LukasKropf/IO-Link-Shield/KiCad/ExportBilder/20171119_PCB_Vorschau_Unten.png

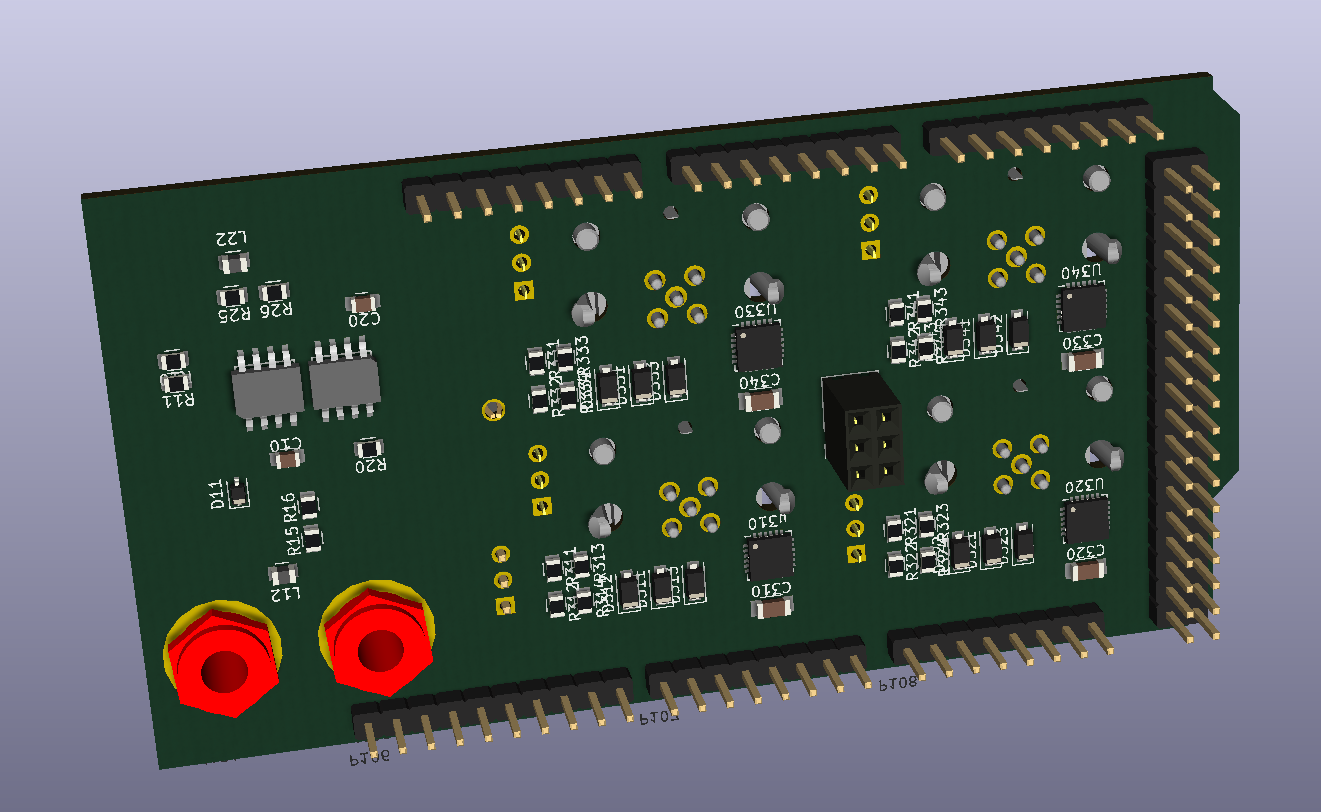
KiCad/ExportBilder/20171119_PCB_Vorschau_Unten.png
