LukasKropf/IO-Link-Shield/KiCad/ExportBilder/20171201_PCB_Vorschau_oben.png

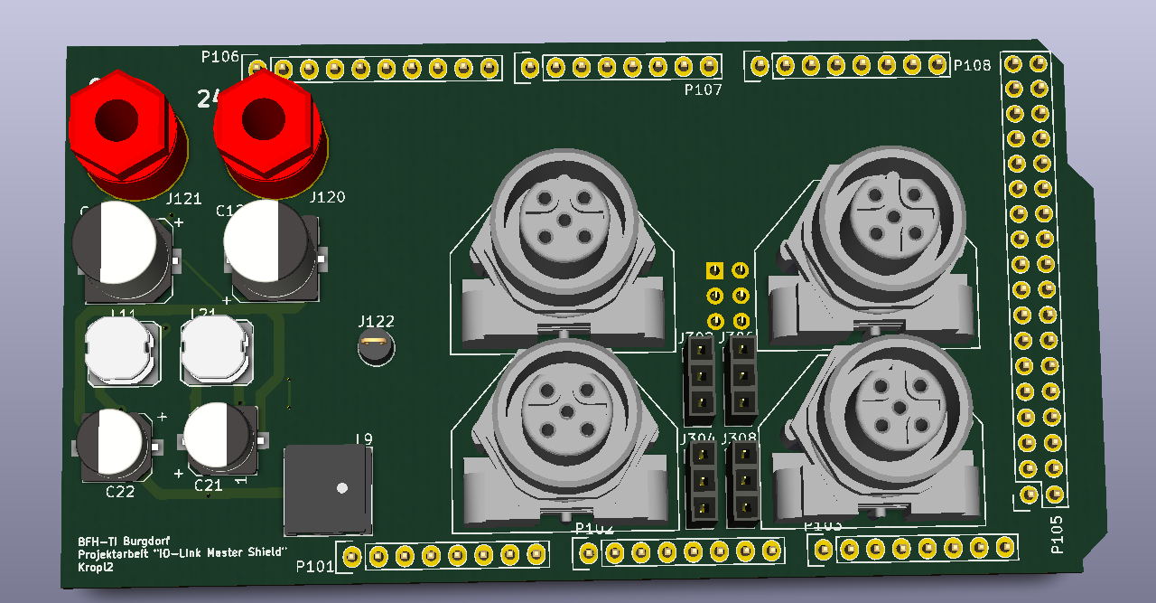
KiCad/ExportBilder/20171201_PCB_Vorschau_oben.png
