LukasKropf/IO-Link-Shield/KiCad/ExportBilder/20171201_PCB_Vorschau_Unten.png

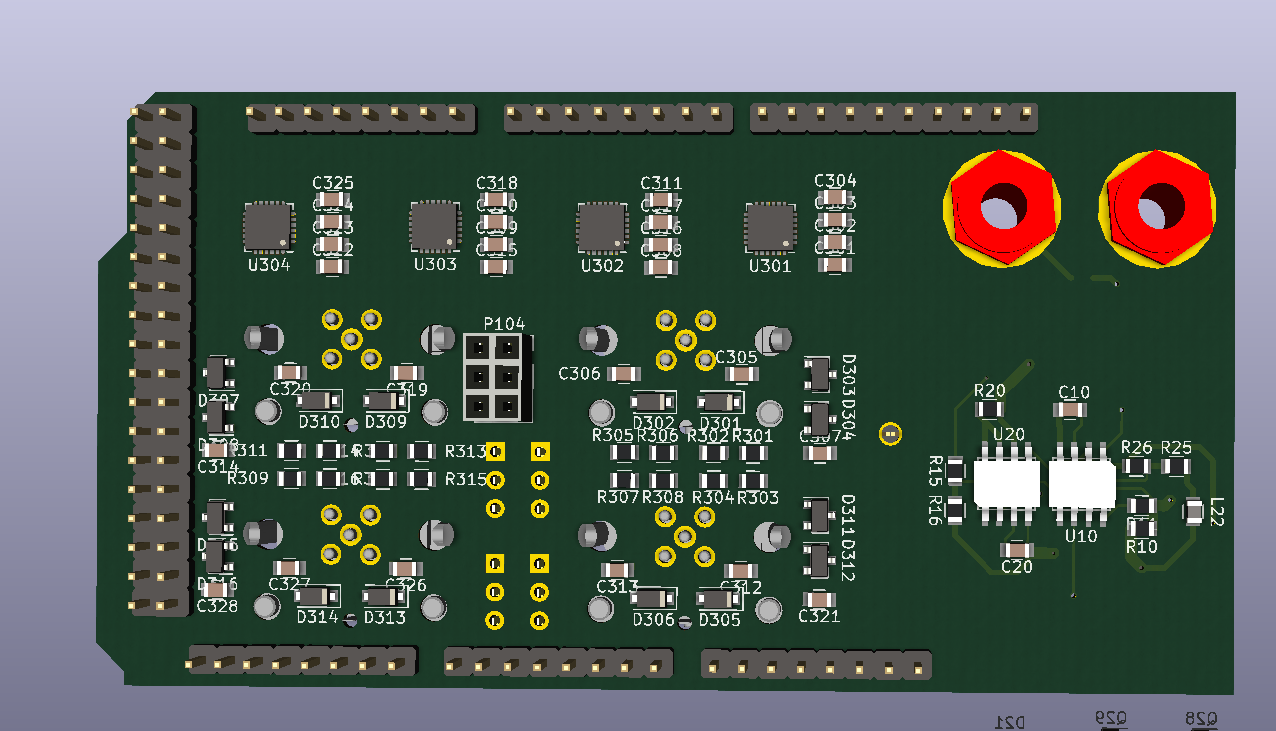
KiCad/ExportBilder/20171201_PCB_Vorschau_Unten.png
