LukasKropf/IO-Link-Shield/KiCad/ExportBilder/TestPoint.png

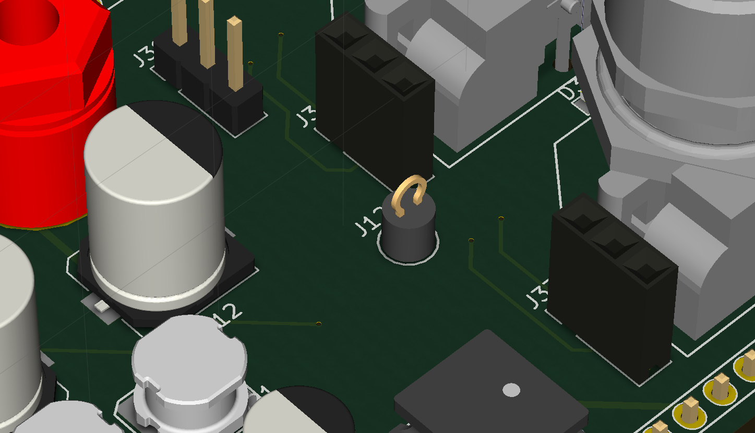
KiCad/ExportBilder/TestPoint.png
