LukasKropf/IO-Link-Shield/Simulationen/BuckBoostConverter/BoostConverter.asc

Arduino: res; 50
C1: polcap; 330µ; V=2.5 Irms=3 Rser=0.006 Lser=0 mfg="Rubycon" pn="2.5SWZ330M R09" type="Al electrolytic"
C2: cap; 100µ
C5: cap; 430p
C6: polcap; 150µ; V=2 Irms=3.87298 Rser=0.018 Lser=0 mfg="KEMET" pn="A700V157M002ATE018" type="Al electrolytic"
C7: cap; 1µ; V=50 Irms=0 Rser=0.005952 Lser=569.87f
D1: schottky; 1N5819
L1: ind; 47µ; Ipk=0.85 Rser=0.123 Rpar=32930 Cpar=2.612p mfg="Bourns, Inc." pn="SRR6040A-470M"
L2: ind; 1µ
R1: res; 180
R2: res; 0.33
R3: res; 200k
R6: res; 1000
R8: res; 11.5k
S1: sw; MySW
V1: voltage; 5v; Rser=0.5
V2: voltage; PULSE(0 24 100ms)
X2: MC33063A
Named nets: 0, 24Vout, 5V, Isns, SWC
.tran 150ms
.inc MC34063.lib
.options Gmin=1e-9  method=Gear
.meas RMScurrentStartup RMS I(V1) FROM 0 TO 70ms
.meas RMScurrentRun RMS I(V1) FROM 80ms TO 100ms
.model MYSW SW(Ron=1 Roff=100Meg Vt=.5 Vh=-.4)
