LukasKropf/IO-Link-Shield/Simulationen/BuckBoostConverter/BuckBoostConverter.asc

Arduino: res; {Rarduino}
C1: polcap; 150µ; V=35 Irms=595m Rser=0.027 Lser=0
C2: polcap; 150µ; V=35 Irms=595m Rser=0.027 Lser=0
C4: polcap; 120µ; V=10 Irms=3.87298 Rser=0.018 Lser=0
C5: cap; 430p
C9: cap; 120p
C10: polcap; 120µ; V=10 Irms=3.87298 Rser=0.018 Lser=0
D1: schottky; 1N5819
D2: schottky; 1N5819
D3: schottky; 1N5819
D4: zener; BZX84C10L
L1: ind; 47µ; Ipk=0.85 Rser=0.123 Rpar=32930 Cpar=2.612p mfg="Bourns, Inc." pn="SRR6040A-470M"
L2: ind; 1000n; Ipk=1.2 Rser=0.12 Rpar=0 Cpar=0 mfg="Murata" pn="LQM31PN1R0M00"
L4: ind; 100µ; Ipk=1.2 Rser=0.12 Rpar=0 Cpar=0
L5: ind; 47µ
L6: ind; 1000n; Ipk=0.9 Rser=0.2 Rpar=1600 Cpar=1.25p mfg="Würth Elektronik" pn="74479763210A WE-PMI 0603"
M1: pmos; BSS84
M2: nmos; NDC7002N
R1: res; 180
R2: res; 0.33
R3: res; 200k
R4: res; 0.25
R5: res; 200k
R6: res; {Rlast}
R7: res; 67k
R8: res; 11.5k
R9: res; 26.1k
R10: res; 100k
S1: sw; MySW
S2: sw; MySW
V1: voltage; 5V; Rser=0.5
V3: voltage; PULSE(0 24 100m)
X1: MC33063A
X2: MC33063A
Named nets: 0, 24Vintern, 5Vint, Isns, SWC, 5V, BoostEnable, 24V
.tran 150ms
.options Gmin=1e-9  method=Gear
.meas RMScurrentStartup RMS I(V1) FROM 0 TO 70ms
.meas RMScurrentRun RMS I(V1) FROM 80ms TO 100ms
.model MYSW SW(Ron=1n Roff=100Meg Vt=.5 Vh=-.4)
;step param Rlast list 400 1000 2k 5k 10k
.param Rlast 1000
.param Rarduino 40
