LukasKropf/IO-Link-Shield/Simulationen/BuckBoostConverter/BuckConverter.asc

Arduino: res; 50
C1: polcap; 120µ; V=10 Irms=3.87298 Rser=0.018 Lser=0
C3: cap; 120p
C6: polcap; 120µ; V=10 Irms=3.87298 Rser=0.018 Lser=0
C8: cap; 149µ
D2: schottky; 1N5819
D3: schottky; 1N5819
L1: ind; 1000n; Ipk=0.9 Rser=0.2 Rpar=1600 Cpar=1.25p mfg="Würth Elektronik" pn="74479763210A WE-PMI 0603"
L5: ind; 47µ
R4: res; 30k
R5: res; 0.25
R7: res; 10k
V3: voltage; 24V
X1: MC33063A
Named nets: 0, 24V, 24Vin, 5Vout
.tran 10ms
.inc MC34063.lib
.options Gmin=1e-9  method=Gear
.meas RMSvoltage5VOut RMS V(5vout) FROM 2ms TO 8ms
