LukasKropf/IO-Link-Shield/Simulationen/BuckBoostConverter/MC33063A.asc

A1: diffschmtbuf; Vt=0; Vh=1m; tripdt={tdt}
A2: diffschmitt; Vt=-0.9 Vh=0.35; trise=50n tfall=0u9; tripdt={tdt}
A3: buf1; ref=0.1 tau=20n; tripdt={tdt}
A4: and; ref=0.9 td=0u2; tripdt={tdt}
A5: srflop; tau=0u1; tripdt={tdt}
C1: cap; 20p
C2: cap; 12p
C3: cap; 10p
C4: cap; 10p
D1: zener; 1V25
D2: diode; Dsub
E1: e; 1
G1: g; 0m5
I1: current; TBL(0 0 2.5 2m8 3.5 3m1 40 3m4)
I3: current; TBL(2 0 3 35u)
Q1: npn; sw
Q2: npn; sw; m=85m
R1: res; 10k
R2: res; 10k
R3: res; 100
R4: res; 1e7
S1: sw; bump
S2: sw; sink
S3: sw; comp
S4: sw; drive
Named nets: DrC, Ipk, Vcc, Inv, SwC, SwE, Osc, Com, COM, 0, 1, A, B, S, R, Q, DrE, 2, ref, 3, osc, C, DrB
.model comp sw level 2
+ Vt=290m Vh=-100m
+ Ron=300 Roff=1e7
+ Ilimit=15m
.model sink sw level 2
+ Vt=0.1 Vh=-1m
+ Ron=1k Roff=1e7
+ Ilimit=255u Vser=0.1
.model bump sw level 2
+ Vt=0.1 Vh=-1m
+ Ron=1e7 Roff=1k
.model 1V25 d Ron=1 Roff=466 Vrev=1.25 revEpsilon=10m
MC33063A
300mV
Isupply
0V 0ma
2.5 2m8
3.5 3m1
40 3m4
Ibias -20nA
(not modeled)
Line Reg: 1.4mV
3V to 40V
Beta=75 1A
Vce=0.45 1A
Tstorage 2us
Rsat 0.48
Ip 35u
Im 220u
Vtp 1.25
Vtm 0.75
1nF 33kHz
.param tdt=10n
I2 S R pulse(5 0 0 1n)
G=4/1.25/10k
force f/f reset at startup
.model Dsub d Ron=1
+ Vfwd=0.6 Epsilon=0.2
.model sw npn Is=50f
+ Rb=1 Re=30m Rc=0.4
+ Bf=130 Br=10 Ikf=1.5
+ Cje=100p Cjc=20p
.model drive sw level 2
+ Vt=300m Vh=-10m
+ Ron=200 Roff=1e8
+ Ilimit=0m7
Rev 2
