LukasKropf/IO-Link-Shield/Simulationen/BuckBoostConverter/TL431AS.asc

C1: cap; 1n; Rpar=700
C2: cap; 40p; Rser=6k Rpar=2e6
D1: diode; Dc
D2: diode; Dc
D3: diode; Dn
D4: diode; Di
D5: zener; 2V5
D6: diode; Dc
G1: g2; 1
G2: g2; 90m
R1: res; 1e6
R2: res; 900k
R3: res; 700k
Named nets: R, K, A, 4, 5, 6, 7
.model Dc d Ron=7 Vfwd=0.6 Vrev=36 epsilon=50m
.model Dn d Is=5p Kf=55f Cjo=0p3
.model Di d Ron=10m epsilon=1m
.model 2V5 d Ron=0.13 Vfwd=0.6 Vrev=2.5 epsilon=10m
+ Roff=7k revepsilon=10m
TL431A
